engee974/discipline/acrylic-case/discipline-open-layer.dxf

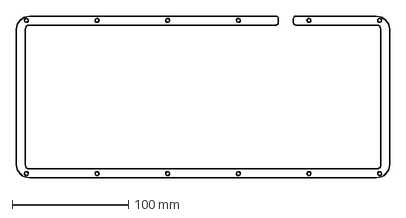
[picture p20: CAD file, 2020-07-10]
acrylic-case/discipline-open-layer.dxf
320.9 x 138.8 mm
