engee974/discipline/acrylic-case/discipline-closed-layer.dxf

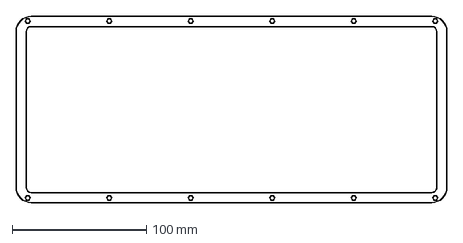
[picture p21: CAD file, 2020-07-10]
acrylic-case/discipline-closed-layer.dxf
320.9 x 138.8 mm
