engee974/discipline/acrylic-case/discipline-foot-2.dxf

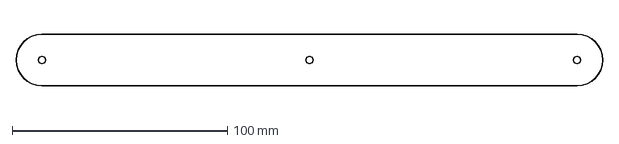
[picture p22: CAD file, 2020-07-10]
acrylic-case/discipline-foot-2.dxf
272.5 x 24.0 mm
